renzorospi/sueno-con-el-cielo-y-el-mar/pcb/pcbv2_etch_silk_bottom.pdf

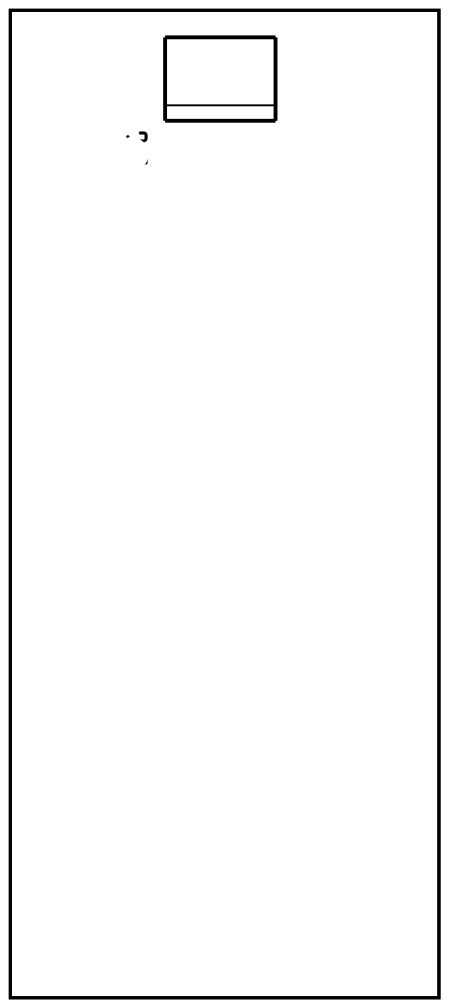
[picture p9: page 1]
