renzorospi/sueno-con-el-cielo-y-el-mar/pcb/pcbv2_etch_silk_bottom_mirror.pdf

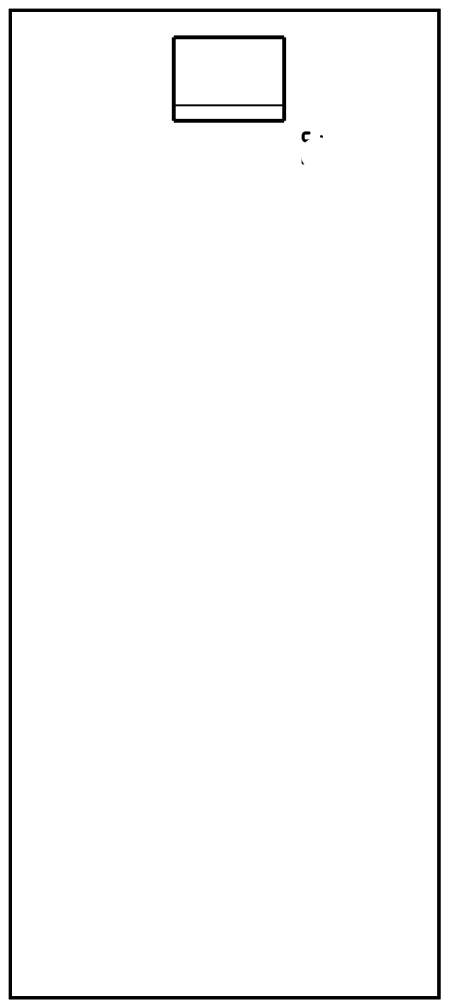
[picture p10: page 1]
