renzorospi/sueno-con-el-cielo-y-el-mar/pcb/pcbv2_etch_silk_top.pdf

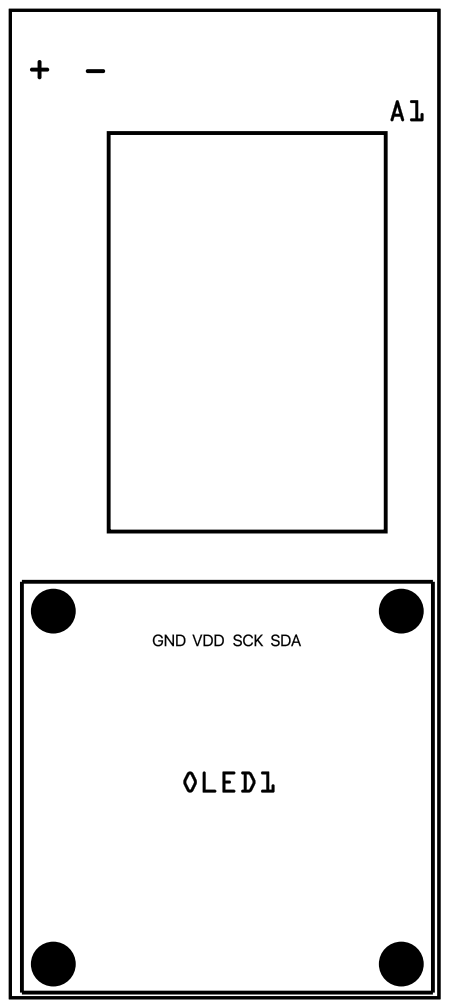
[picture p11: page 1]
