renzorospi/sueno-con-el-cielo-y-el-mar/pcb/pcbv2_etch_silk_top_mirror.pdf

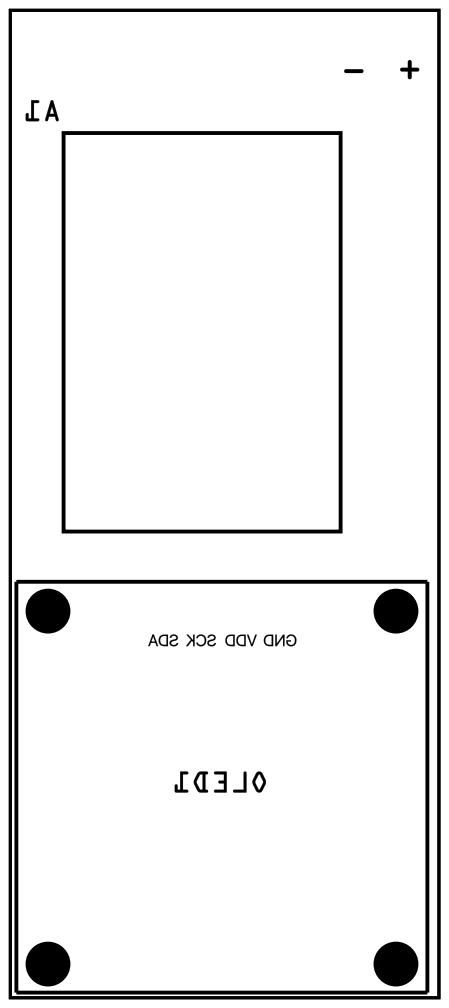
[picture p12: page 1]
